CuriousLad1000/HMI_interface_for_PC/UI Design files/FAN/Fan_speed.png

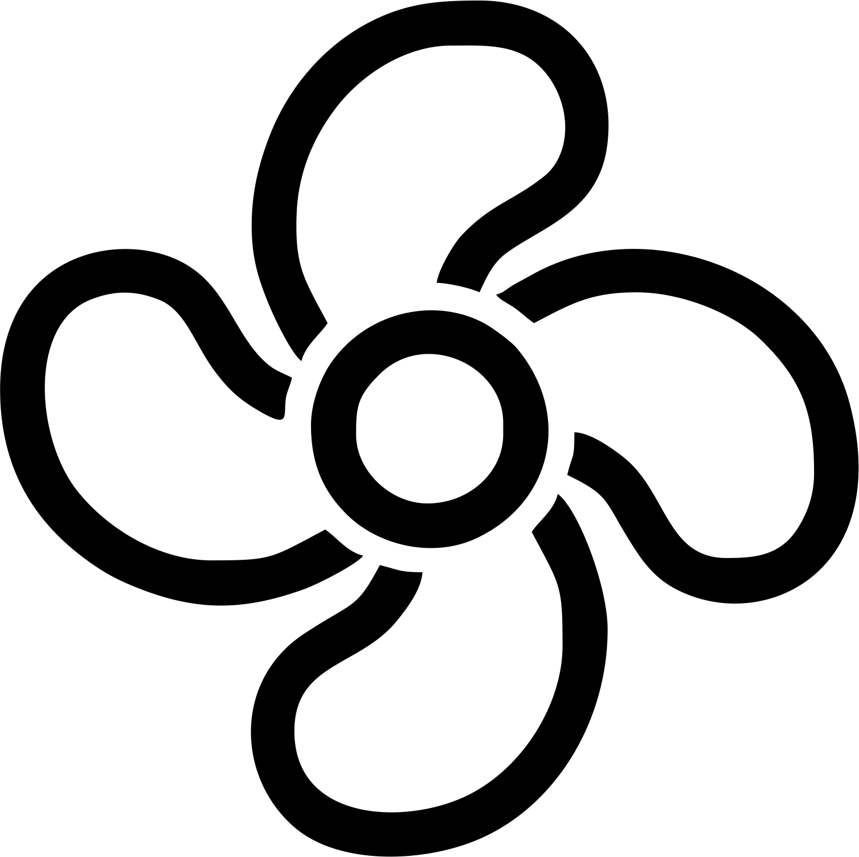
UI Design files/FAN/Fan_speed.png
