CuriousLad1000/HMI_interface_for_PC/UI Design files/FAN/tst.png

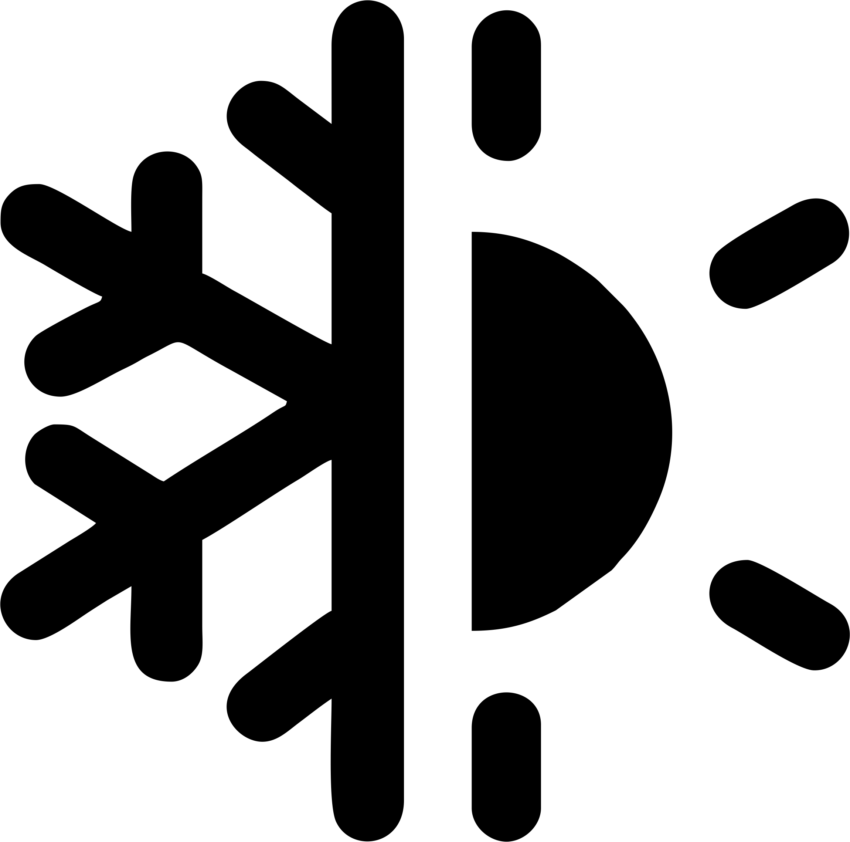
UI Design files/FAN/tst.png
