CuriousLad1000/HMI_interface_for_PC/UI Design files/HOME/Home2.png

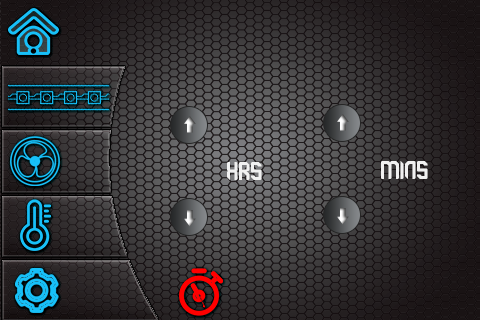
UI Design files/HOME/Home2.png
