CuriousLad1000/HMI_interface_for_PC/UI Design files/HOME/Home_OFF.png

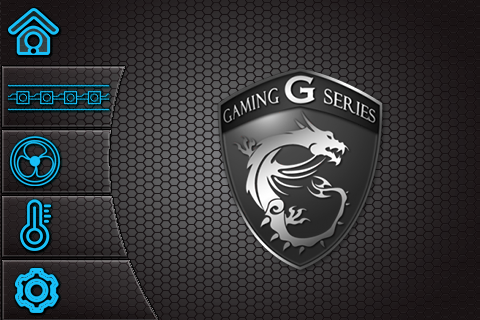
UI Design files/HOME/Home_OFF.png
