CuriousLad1000/HMI_interface_for_PC/UI Design files/LED/OFF_Glow.png

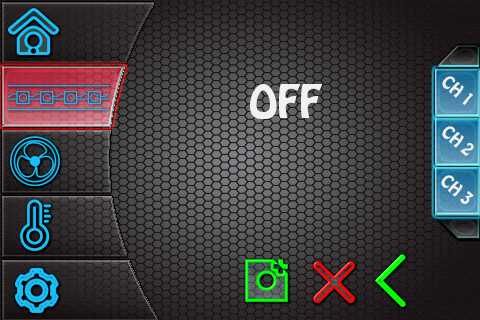
UI Design files/LED/OFF_Glow.png
