CuriousLad1000/HMI_interface_for_PC/UI Design files/LED/Untitled-1.png

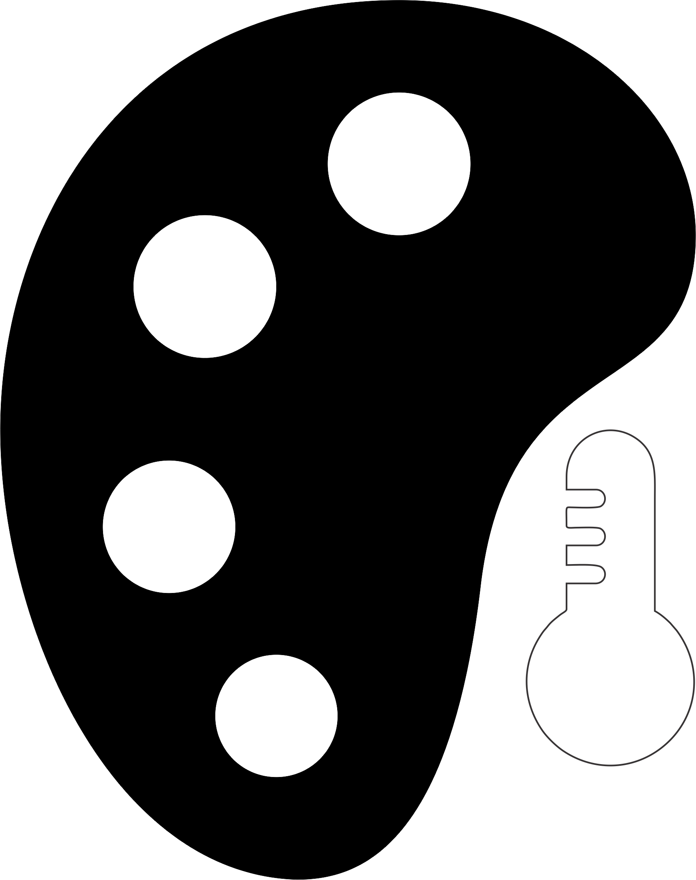
UI Design files/LED/Untitled-1.png
