CuriousLad1000/HMI_interface_for_PC/UI Design files/Res/gui idea.jpg

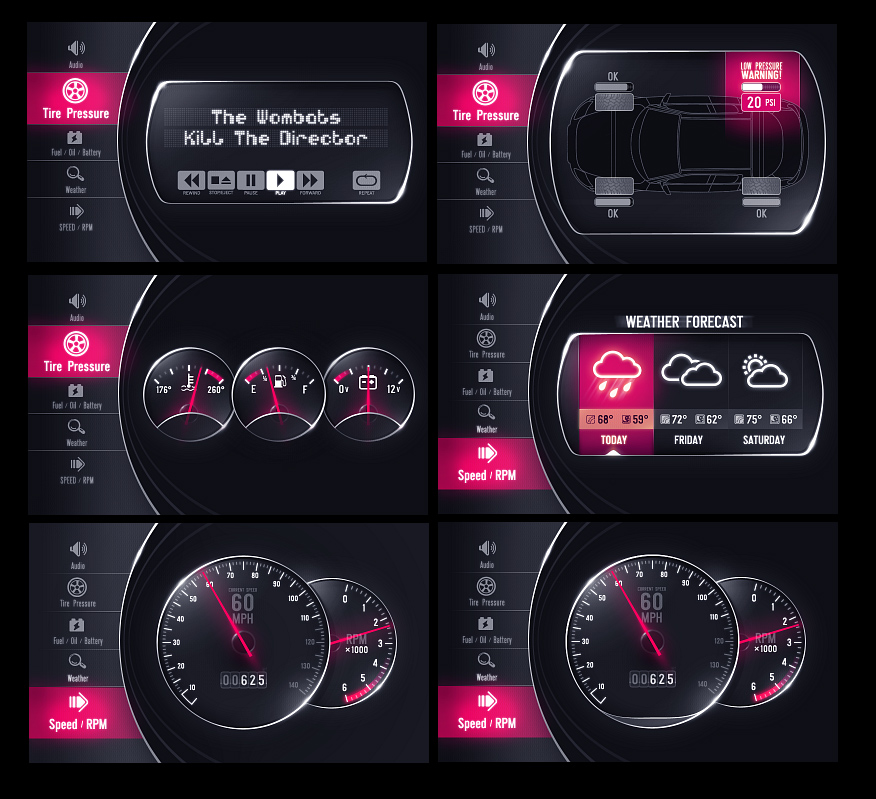
UI Design files/Res/gui idea.jpg
