CuriousLad1000/HMI_interface_for_PC/UI Design files/Res/UI tst.png

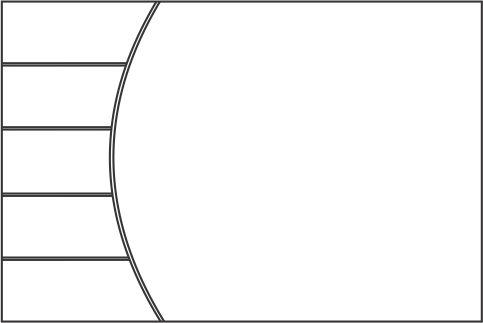
UI Design files/Res/UI tst.png
