CuriousLad1000/HMI_interface_for_PC/UI Design files/Res/Untitled-1.png

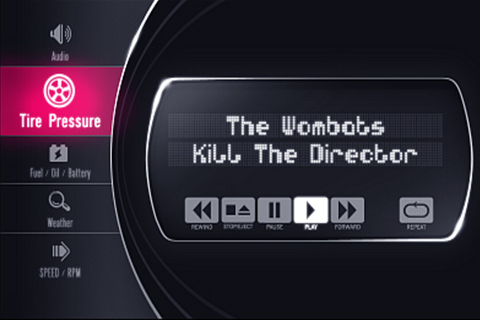
UI Design files/Res/Untitled-1.png
