CuriousLad1000/HMI_interface_for_PC/UI Design files/SETTINGS/SET_1_glow.png

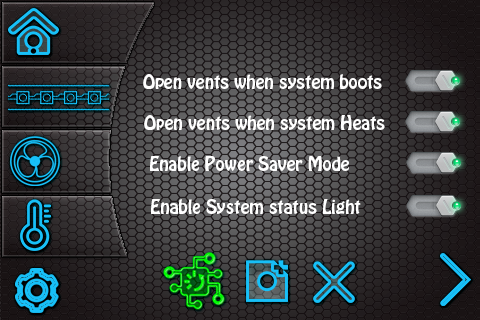
UI Design files/SETTINGS/SET_1_glow.png
